minimoc/minimoc/firmware/graphics.h

#pragma once

// LOGO VERVEINE
// Bitmap 64x64 (XBM format compatible U8g2)
// -----------------------------------------------------------------
// LOGO VERVEINE STYLISÉ (64x64) - FORMAT XBM (LSB First)
// Garanti sans décalage géométrique avec u8g2.drawXBMP
// -----------------------------------------------------------------
#define logo_verveine_width 64
#define logo_verveine_height 64
const unsigned char logo_verveine_bits[] PROGMEM = {
	0x00, 0x00, 0x00, 0x00, 0x00, 0x00, 0x00, 0x00, 0x00, 0x00, 0x00, 0x00, 0x00, 0x00, 0x00, 0x00, 
	0x00, 0x00, 0x00, 0x00, 0x00, 0x00, 0x00, 0x00, 0x00, 0x00, 0x00, 0x00, 0x00, 0x00, 0x00, 0x00, 
	0x00, 0x00, 0x00, 0x00, 0x00, 0x00, 0x00, 0x00, 0x00, 0x00, 0x00, 0x00, 0x00, 0x00, 0x00, 0x00, 
	0x00, 0x00, 0x00, 0x00, 0x00, 0x00, 0xf0, 0x03, 0x00, 0x00, 0x00, 0x00, 0x00, 0x00, 0xfe, 0x03, 
	0x00, 0x00, 0x00, 0x00, 0x00, 0xc0, 0x87, 0x02, 0x00, 0x00, 0x00, 0x00, 0x00, 0xf8, 0x60, 0x02, 
	0x00, 0x00, 0x00, 0x00, 0x00, 0x1f, 0x60, 0x03, 0x00, 0x00, 0x00, 0x00, 0xe0, 0x07, 0x11, 0x03, 
	0x00, 0x00, 0x00, 0x00, 0xf8, 0x00, 0x09, 0x03, 0x00, 0x00, 0x00, 0x00, 0x3c, 0x00, 0x05, 0x03, 
	0x00, 0x00, 0x00, 0x80, 0x8f, 0x00, 0x81, 0x01, 0x00, 0x00, 0x00, 0xc0, 0x83, 0x00, 0x80, 0x01, 
	0x00, 0x00, 0x00, 0x70, 0x40, 0x10, 0xb3, 0x00, 0x00, 0x00, 0x00, 0x3c, 0x44, 0x10, 0xc0, 0x00, 
	0x00, 0x00, 0x00, 0x0e, 0x42, 0x30, 0xc0, 0x00, 0x00, 0x00, 0x80, 0x03, 0x42, 0x18, 0xc0, 0x00, 
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
  u8g2.drawXBMP(32, 0, logo_verveine_width, logo_verveine_height, logo_verveine_bits);

  // version en bas à gauche (zone libre 32×64 px)
  u8g2.setFont(u8g2_font_5x7_tf);
  int vw = u8g2.getStrWidth(FIRMWARE_VERSION);
  u8g2.drawStr((32 - vw) / 2, 62, FIRMWARE_VERSION);

  u8g2.sendBuffer();
}
